elementchen/VoxTriple_Classic/3d_print/Thin/cover.stl

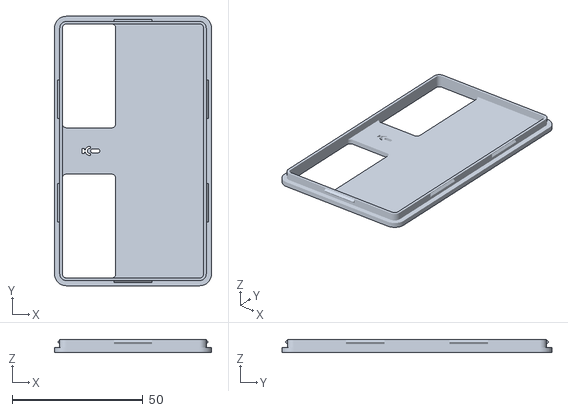
[picture p15: CAD file, 2026-09-11]
3d_print/Thin/cover.stl
60.0 x 103.0 x 5.00
