elementchen/VoxTriple_Classic/3d_print/Minimal/test1.stl

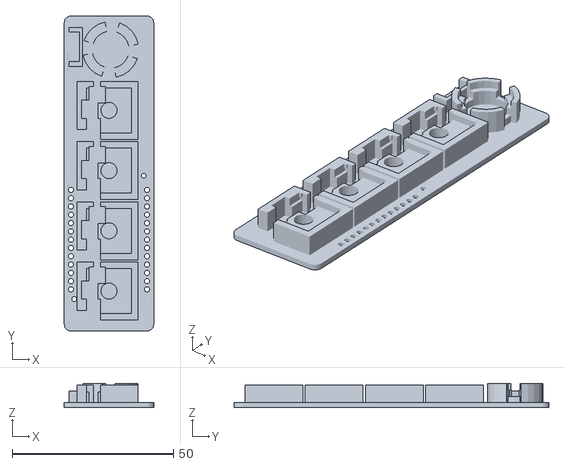
[picture p16: CAD file, 2026-09-13]
3d_print/Minimal/test1.stl
27.8 x 97.8 x 7.50
