elementchen/VoxTriple_Classic/3d_print/Thin/cover_3.stl

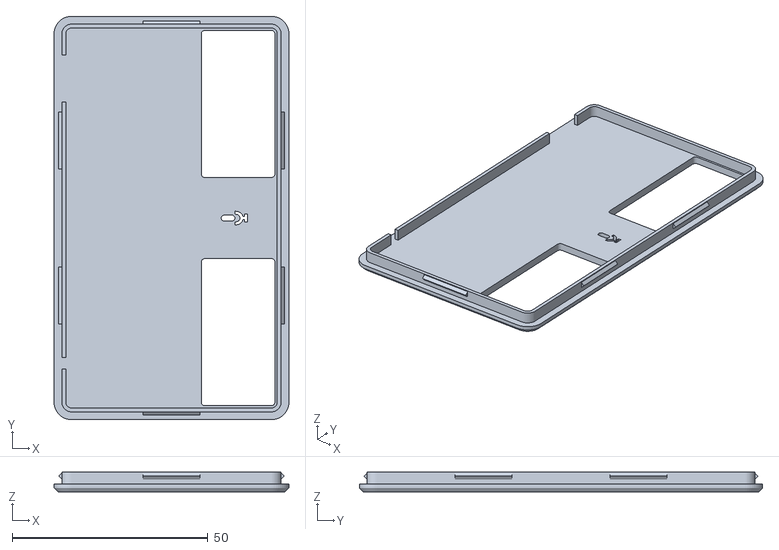
[picture p17: CAD file, 2026-09-11]
3d_print/Thin/cover_3.stl
60.0 x 103.0 x 5.00
