elementchen/VoxTriple_Classic/3d_print/Minimal/test0.stl

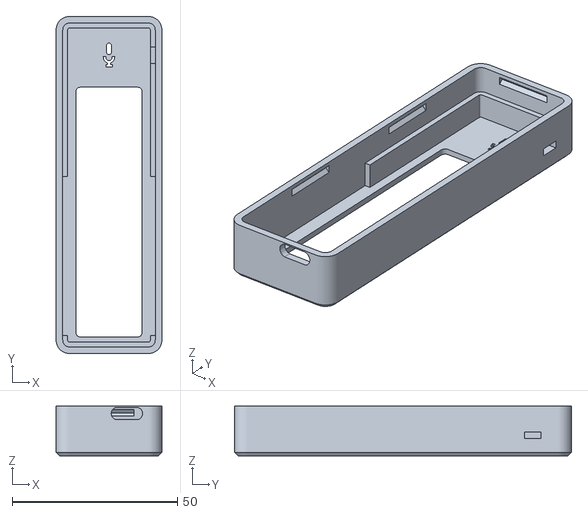
[picture p18: CAD file, 2026-09-13]
3d_print/Minimal/test0.stl
32.0 x 102.0 x 15.0
