elementchen/VoxTriple_Classic/3d_print/Thin/cover_tilt_2.stl

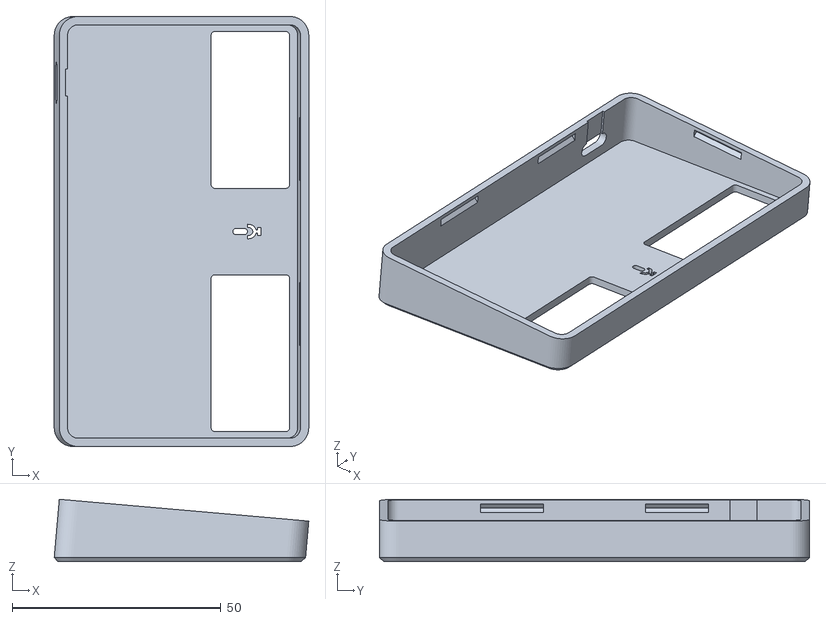
[picture p19: CAD file, 2026-09-11]
3d_print/Thin/cover_tilt_2.stl
61.0 x 103.0 x 15.0
