elementchen/VoxTriple_Classic/3d_print/Minimal/test_all.3mf

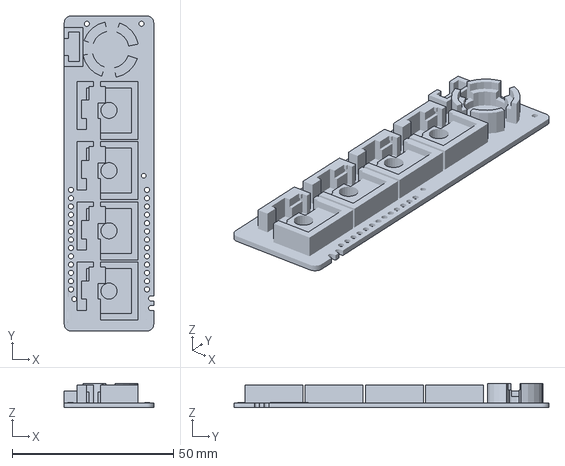
[picture p20: CAD file, 2026-09-13]
3d_print/Minimal/test_all.3mf
27.8 x 97.8 x 7.50 mm
