elementchen/VoxTriple_Classic/3d_print/Minimal/test3.stl

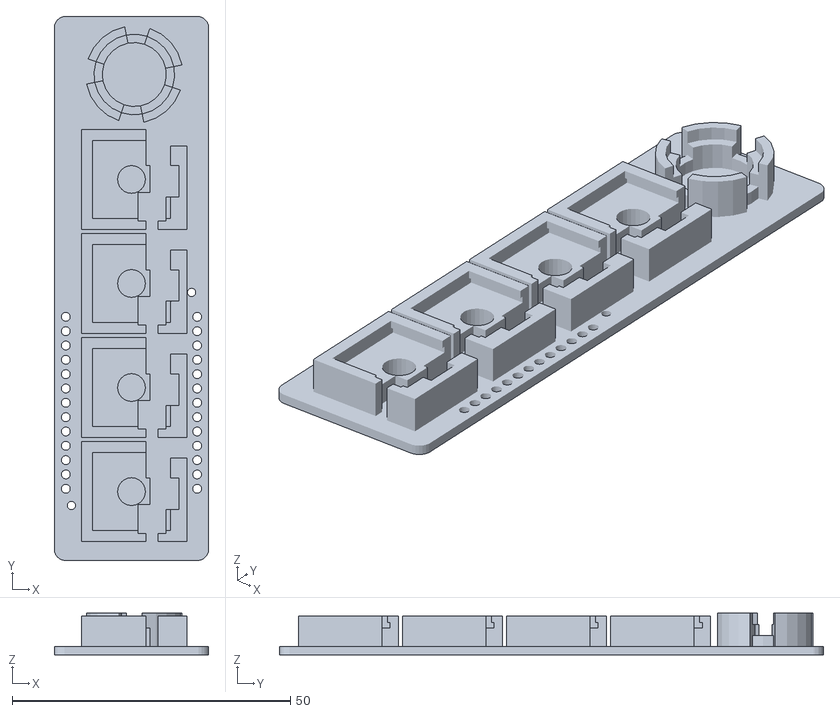
[picture p21: CAD file, 2026-09-11]
3d_print/Minimal/test3.stl
27.8 x 97.8 x 7.50
