elementchen/VoxTriple_Classic/3d_print/Minimal/test.3mf

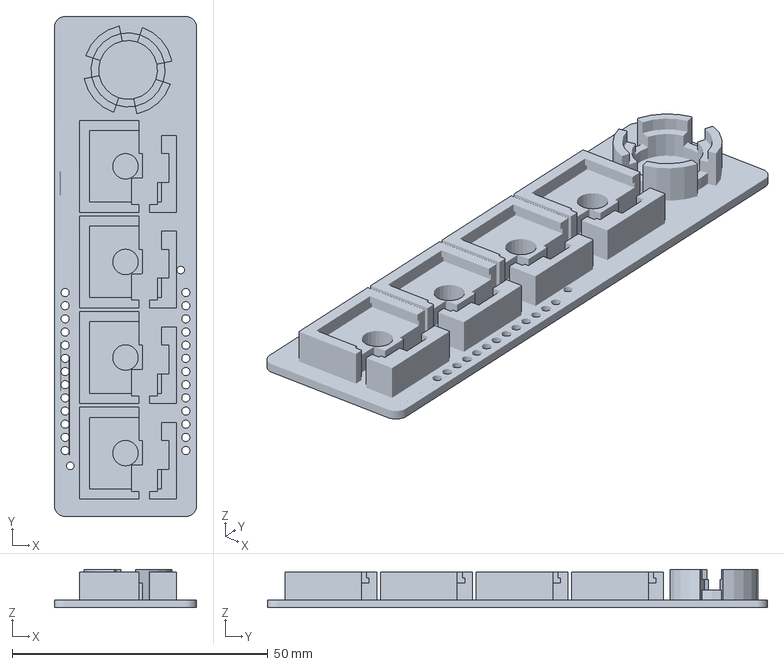
[picture p22: CAD file, 2026-09-11]
3d_print/Minimal/test.3mf
27.8 x 97.8 x 7.50 mm
