elementchen/VoxTriple_Classic/3d_print/Minimal/test2.stl

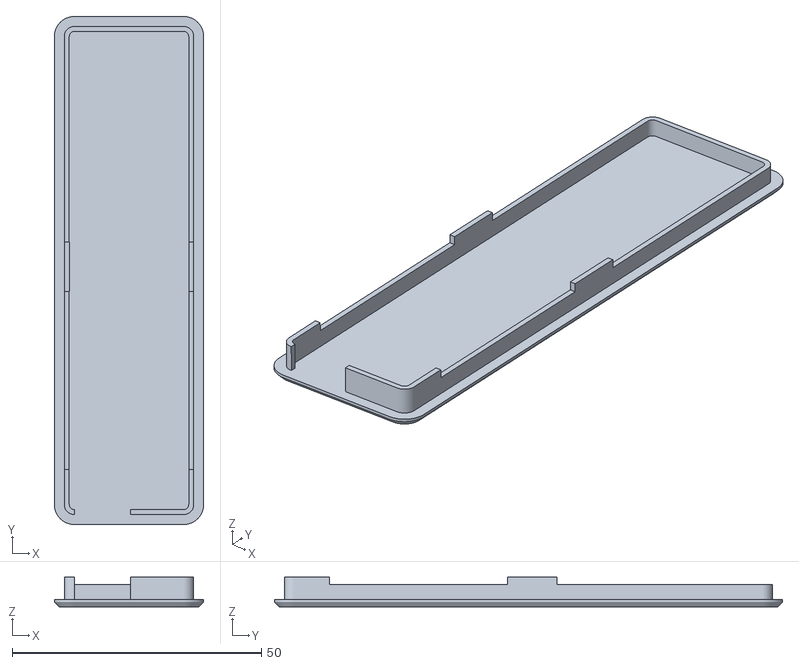
[picture p23: CAD file, 2026-09-11]
3d_print/Minimal/test2.stl
30.0 x 102.0 x 6.02
