elementchen/VoxTriple_Classic/esp32_bt_mic/src/config_storage.c

/*
 * SPDX-FileCopyrightText: 2024 ESP32 BT Microphone Project
 *
 * SPDX-License-Identifier: Unlicense OR CC0-1.0
 */

#include <stdint.h>
#include <string.h>
#include "nvs.h"
#include "nvs_flash.h"
#include "esp_log.h"
#include "config_storage.h"

static const char *TAG = "CONFIG_STORAGE";

/* Default button mappings (Windows VK codes) */
static const uint8_t s_default_vk[BUTTON_NUM] = {
    0x0D,  /* VK_RETURN (Enter) */
    0x1B,  /* VK_ESCAPE (Esc) */
    0x20,  /* VK_SPACE (Space) */
    0x09,  /* VK_TAB (Tab) */
};

static const uint8_t s_default_mod[BUTTON_NUM] = {
    0x00,  /* No modifier */
    0x00,
    0x00,
    0x00,
};

static const char *s_nvs_keys[BUTTON_NUM] = {
    NVS_KEY_BTN1_MAP,
    NVS_KEY_BTN2_MAP,
    NVS_KEY_BTN3_MAP,
    NVS_KEY_BTN4_MAP,
};

void config_storage_init(void)
{
    ESP_LOGI(TAG, "Initializing configuration storage");

    /* Try to load each button mapping; if not found, save defaults */
    for (int i = 0; i < BUTTON_NUM; i++) {
        uint8_t vk_code = 0, modifier = 0;
        esp_err_t ret = config_storage_load_button(i, &vk_code, &modifier);
        if (ret != ESP_OK) {
            ESP_LOGI(TAG, "Button %d: no saved config, setting defaults (VK=0x%02X, MOD=0x%02X)",
                     i + 1, s_default_vk[i], s_default_mod[i]);
            config_storage_save_button(i, s_default_vk[i], s_default_mod[i]);
        } else {
            ESP_LOGI(TAG, "Button %d: loaded config (VK=0x%02X, MOD=0x%02X)",
                     i + 1, vk_code, modifier);
        }
    }

    /* Initialize sleep_mode default configuration (default to 1) */
    uint8_t sleep_mode = 0;
    if (config_storage_load_sleep_mode(&sleep_mode) != ESP_OK) {
        ESP_LOGI(TAG, "Sleep mode: no saved config, setting default (enabled)");
        config_storage_save_sleep_mode(1);
    }

    /* Initialize mic_enabled default configuration (default to 1) */
    uint8_t mic_enabled = 0;
    if (config_storage_load_mic_enabled(&mic_enabled) != ESP_OK) {
        ESP_LOGI(TAG, "Mic enabled: no saved config, setting default (enabled)");
        config_storage_save_mic_enabled(1);
    }
}

esp_err_t config_storage_save_button(uint8_t button_id, uint8_t vk_code, uint8_t modifier)
{
    if (button_id >= BUTTON_NUM) {
        return ESP_ERR_INVALID_ARG;
    }

    nvs_handle_t nvs_handle;
    esp_err_t ret = nvs_open(NVS_NAMESPACE, NVS_READWRITE, &nvs_handle);
    if (ret != ESP_OK) {
        ESP_LOGE(TAG, "NVS open failed: %s", esp_err_to_name(ret));
        return ret;
    }

    /* Store as 2-byte blob: [vk_code, modifier] */
    uint8_t data[2] = {vk_code, modifier};
    ret = nvs_set_blob(nvs_handle, s_nvs_keys[button_id], data, sizeof(data));

    if (ret == ESP_OK) {
        ret = nvs_commit(nvs_handle);
    }

    nvs_close(nvs_handle);

    if (ret != ESP_OK) {
        ESP_LOGE(TAG, "NVS save button %d failed: %s", button_id + 1, esp_err_to_name(ret));
    } else {
        ESP_LOGI(TAG, "Saved button %d mapping: VK=0x%02X, MOD=0x%02X",
                 button_id + 1, vk_code, modifier);
    }

    return ret;
}

esp_err_t config_storage_load_button(uint8_t button_id, uint8_t *vk_code, uint8_t *modifier)
{
    if (button_id >= BUTTON_NUM || !vk_code || !modifier) {
        return ESP_ERR_INVALID_ARG;
    }

    nvs_handle_t nvs_handle;
    esp_err_t ret = nvs_open(NVS_NAMESPACE, NVS_READONLY, &nvs_handle);
    if (ret != ESP_OK) {
        ESP_LOGW(TAG, "NVS open failed: %s", esp_err_to_name(ret));
        return ret;
    }

    uint8_t data[2] = {0, 0};
    size_t length = sizeof(data);

    ret = nvs_get_blob(nvs_handle, s_nvs_keys[button_id], data, &length);
    if (ret == ESP_OK && length == sizeof(data)) {
        *vk_code = data[0];
        *modifier = data[1];
    } else {
        *vk_code = s_default_vk[button_id];
        *modifier = s_default_mod[button_id];
    }

    nvs_close(nvs_handle);
    return ret;
}

#define NVS_KEY_HFP_ADDR "hfp_addr"

esp_err_t config_storage_save_hfp_addr(esp_bd_addr_t addr)
{
    nvs_handle_t nvs_handle;
    esp_err_t ret = nvs_open(NVS_NAMESPACE, NVS_READWRITE, &nvs_handle);
    if (ret != ESP_OK) return ret;

    ret = nvs_set_blob(nvs_handle, NVS_KEY_HFP_ADDR, addr, ESP_BD_ADDR_LEN);
    if (ret == ESP_OK) nvs_commit(nvs_handle);
    nvs_close(nvs_handle);

    if (ret == ESP_OK) {
        ESP_LOGI(TAG, "HFP addr saved: %02x:%02x:%02x:%02x:%02x:%02x",
                 addr[0], addr[1], addr[2], addr[3], addr[4], addr[5]);
    }
    return ret;
}

esp_err_t config_storage_load_hfp_addr(esp_bd_addr_t addr)
{
    nvs_handle_t nvs_handle;
    esp_err_t ret = nvs_open(NVS_NAMESPACE, NVS_READONLY, &nvs_handle);
    if (ret != ESP_OK) return ret;

    size_t len = ESP_BD_ADDR_LEN;
    ret = nvs_get_blob(nvs_handle, NVS_KEY_HFP_ADDR, addr, &len);
    nvs_close(nvs_handle);
    return ret;
}

esp_err_t config_storage_clear_hfp_addr(void)
{
    nvs_handle_t nvs_handle;
    esp_err_t ret = nvs_open(NVS_NAMESPACE, NVS_READWRITE, &nvs_handle);
    if (ret != ESP_OK) return ret;

    ret = nvs_erase_key(nvs_handle, NVS_KEY_HFP_ADDR);
    if (ret == ESP_OK || ret == ESP_ERR_NVS_NOT_FOUND) {
        nvs_commit(nvs_handle);
        ret = ESP_OK;
    }
    nvs_close(nvs_handle);
    ESP_LOGI(TAG, "HFP host address cleared from NVS.");
    return ret;
}

#define NVS_KEY_TX_POWER   "tx_power"
#define NVS_KEY_SLEEP_MODE "sleep_mode"

esp_err_t config_storage_save_tx_power(uint8_t level)
{
    nvs_handle_t nvs_handle;
    esp_err_t ret = nvs_open(NVS_NAMESPACE, NVS_READWRITE, &nvs_handle);
    if (ret != ESP_OK) return ret;

    ret = nvs_set_u8(nvs_handle, NVS_KEY_TX_POWER, level);
    if (ret == ESP_OK) nvs_commit(nvs_handle);
    nvs_close(nvs_handle);

    if (ret == ESP_OK) {
        ESP_LOGI(TAG, "TX power level saved: %d", level);
    }
    return ret;
}

esp_err_t config_storage_load_tx_power(uint8_t *level)
{
    if (!level) return ESP_ERR_INVALID_ARG;

    nvs_handle_t nvs_handle;
    esp_err_t ret = nvs_open(NVS_NAMESPACE, NVS_READONLY, &nvs_handle);
    if (ret != ESP_OK) return ret;

    ret = nvs_get_u8(nvs_handle, NVS_KEY_TX_POWER, level);
    nvs_close(nvs_handle);
    return ret;
}

esp_err_t config_storage_save_sleep_mode(uint8_t enabled)
{
    nvs_handle_t nvs_handle;
    esp_err_t ret = nvs_open(NVS_NAMESPACE, NVS_READWRITE, &nvs_handle);
    if (ret != ESP_OK) return ret;

    ret = nvs_set_u8(nvs_handle, NVS_KEY_SLEEP_MODE, enabled);
    if (ret == ESP_OK) nvs_commit(nvs_handle);
    nvs_close(nvs_handle);

    if (ret == ESP_OK) {
        ESP_LOGI(TAG, "Sleep mode saved: %s", enabled ? "enabled" : "disabled");
    }
    return ret;
}

esp_err_t config_storage_load_sleep_mode(uint8_t *enabled)
{
    if (!enabled) return ESP_ERR_INVALID_ARG;

    nvs_handle_t nvs_handle;
    esp_err_t ret = nvs_open(NVS_NAMESPACE, NVS_READONLY, &nvs_handle);
    if (ret != ESP_OK) return ret;

    ret = nvs_get_u8(nvs_handle, NVS_KEY_SLEEP_MODE, enabled);
    nvs_close(nvs_handle);
    return ret;
}

esp_err_t config_storage_save_mic_enabled(uint8_t enabled)
{
    nvs_handle_t nvs_handle;
    esp_err_t ret = nvs_open(NVS_NAMESPACE, NVS_READWRITE, &nvs_handle);
    if (ret != ESP_OK) return ret;

    ret = nvs_set_u8(nvs_handle, NVS_KEY_MIC_ENABLED, enabled);
    if (ret == ESP_OK) nvs_commit(nvs_handle);
    nvs_close(nvs_handle);
    if (ret == ESP_OK) {
        ESP_LOGI(TAG, "Mic enabled configuration saved: %d", enabled);
    }
    return ret;
}

esp_err_t config_storage_load_mic_enabled(uint8_t *enabled)
{
    if (!enabled) return ESP_ERR_INVALID_ARG;

    nvs_handle_t nvs_handle;
    esp_err_t ret = nvs_open(NVS_NAMESPACE, NVS_READONLY, &nvs_handle);
    if (ret != ESP_OK) return ret;

    ret = nvs_get_u8(nvs_handle, NVS_KEY_MIC_ENABLED, enabled);
    nvs_close(nvs_handle);
    return ret;
}

esp_err_t config_storage_clear_all(void)
{
    nvs_handle_t nvs_handle;
    esp_err_t ret = nvs_open(NVS_NAMESPACE, NVS_READWRITE, &nvs_handle);
    if (ret != ESP_OK) return ret;

    ret = nvs_erase_all(nvs_handle);
    if (ret == ESP_OK) nvs_commit(nvs_handle);
    nvs_close(nvs_handle);
    ESP_LOGI(TAG, "Config storage cleared successfully.");
    return ret;
}

esp_err_t config_storage_save_ota_ready(uint8_t ready)
{
    nvs_handle_t nvs_handle;
    esp_err_t ret = nvs_open(NVS_NAMESPACE, NVS_READWRITE, &nvs_handle);
    if (ret != ESP_OK) return ret;

    ret = nvs_set_u8(nvs_handle, NVS_KEY_OTA_READY, ready);
    if (ret == ESP_OK) nvs_commit(nvs_handle);
    nvs_close(nvs_handle);
    if (ret == ESP_OK) {
        ESP_LOGI(TAG, "OTA Ready flag saved: %d", ready);
    }
    return ret;
}

esp_err_t config_storage_load_ota_ready(uint8_t *ready)
{
    if (!ready) return ESP_ERR_INVALID_ARG;

    nvs_handle_t nvs_handle;
    esp_err_t ret = nvs_open(NVS_NAMESPACE, NVS_READONLY, &nvs_handle);
    if (ret != ESP_OK) return ret;

    ret = nvs_get_u8(nvs_handle, NVS_KEY_OTA_READY, ready);
    nvs_close(nvs_handle);
    return ret;
}

esp_err_t config_storage_save_board_model(uint8_t model)
{
    nvs_handle_t nvs_handle;
    esp_err_t ret = nvs_open(NVS_NAMESPACE, NVS_READWRITE, &nvs_handle);
    if (ret != ESP_OK) return ret;

    ret = nvs_set_u8(nvs_handle, NVS_KEY_BOARD_MODEL, model);
    if (ret == ESP_OK) nvs_commit(nvs_handle);
    nvs_close(nvs_handle);
    if (ret == ESP_OK) {
        ESP_LOGI(TAG, "Board model saved: %d", model);
    }
    return ret;
}

esp_err_t config_storage_load_board_model(uint8_t *model)
{
    if (!model) return ESP_ERR_INVALID_ARG;

    nvs_handle_t nvs_handle;
    esp_err_t ret = nvs_open(NVS_NAMESPACE, NVS_READONLY, &nvs_handle);
    if (ret != ESP_OK) return ret;

    ret = nvs_get_u8(nvs_handle, NVS_KEY_BOARD_MODEL, model);
    nvs_close(nvs_handle);
    return ret;
}

esp_err_t config_storage_save_sleep_timeout(uint8_t minutes)
{
    nvs_handle_t nvs_handle;
    esp_err_t ret = nvs_open(NVS_NAMESPACE, NVS_READWRITE, &nvs_handle);
    if (ret != ESP_OK) return ret;

    ret = nvs_set_u8(nvs_handle, NVS_KEY_SLEEP_TIMEOUT, minutes);
    if (ret == ESP_OK) nvs_commit(nvs_handle);
    nvs_close(nvs_handle);
    if (ret == ESP_OK) {
        ESP_LOGI(TAG, "Sleep timeout saved: %d min", minutes);
    }
    return ret;
}

esp_err_t config_storage_load_sleep_timeout(uint8_t *minutes)
{
    if (!minutes) return ESP_ERR_INVALID_ARG;

    nvs_handle_t nvs_handle;
    esp_err_t ret = nvs_open(NVS_NAMESPACE, NVS_READONLY, &nvs_handle);
    if (ret != ESP_OK) return ret;

    ret = nvs_get_u8(nvs_handle, NVS_KEY_SLEEP_TIMEOUT, minutes);
    nvs_close(nvs_handle);
    return ret;
}
