elementchen/VoxTriple_Classic/windows_app_python/spp_client.py

"""Classic Bluetooth SPP Client for VoxTriple.

Replaces the BleClient (ble_client.py) using pyserial.
Bridges serial sync-read thread to asyncio futures for smooth GUI interaction.
"""
import os
import sys
import re
import asyncio
import json
import logging
import threading
import serial
import serial.tools.list_ports

log = logging.getLogger(__name__)


class _EsptoolProgressWriter:
    """Captures esptool stdout to extract flash write percentage and invoke GUI progress callback."""
    def __init__(self, orig_stdout, total_size, cb=None):
        self.orig_stdout = orig_stdout
        self.total_size = total_size
        self.cb = cb
        self.pct_re = re.compile(r'\((\d+)\s*%\)')
        self.encoding = getattr(orig_stdout, "encoding", "utf-8") or "utf-8"
        self.errors = getattr(orig_stdout, "errors", "replace") or "replace"

    def isatty(self):
        return False

    def write(self, text):
        if self.orig_stdout:
            try:
                self.orig_stdout.write(text)
            except Exception:
                pass
        m = self.pct_re.search(text)
        if m:
            pct = int(m.group(1))
            if self.cb:
                written = int(self.total_size * pct / 100)
                try:
                    self.cb(written, self.total_size)
                except Exception:
                    pass

    def flush(self):
        if self.orig_stdout:
            try:
                self.orig_stdout.flush()
            except Exception:
                pass


class SppClient:
    """Connects to ESP32 SPP server via virtual COM port."""

    def __init__(self):
        self._ser = None
        self._port = None
        self._connected = False
        self._read_thread = None
        self._loop = None
        
        # Callbacks registered by the GUI
        self.on_button_event = None   # callback(button_id: int, state: int)
        self.on_status = None         # callback(hfp: int, audio: int)

        # Future used to wait for responses of commands
        self._response_future = None
        
        # Local configuration cache populated on connection
        self._config_cache = {}
        
        # OTA mode flag and queue for flow control
        self._ota_mode = False
        self._ota_queue = asyncio.Queue()

    @property
    def is_connected(self) -> bool:
        return self._connected

    @property
    def address(self) -> str | None:
        """Expose the current COM port name to mimic the original BLE address API."""
        return self._port

    @staticmethod
    def list_ports() -> list[dict]:
        """List all COM ports, sorting likely Bluetooth ports to the top."""
        ports = serial.tools.list_ports.comports()
        result = []
        for p in ports:
            name = p.device
            desc = p.description or ""
            hwid = p.hwid or ""
            
            # Identify potential bluetooth virtual serial ports
            is_bt = False
            bt_keywords = ["bluetooth", "btport", "bthenum", "蓝牙", "标准串行"]
            if any(kw in desc.lower() or kw in hwid.lower() for kw in bt_keywords):
                is_bt = True
                
            result.append({
                "port": name,
                "desc": f"{name} ({desc})",
                "is_bt": is_bt
            })
            
        # Sort so that Bluetooth ports appear first
        result.sort(key=lambda x: x["is_bt"], reverse=True)
        return result

    async def connect(self, port: str) -> bool:
        """Open the serial port, start the read thread, and fetch configuration."""
        try:
            log.info(f"Connecting to serial port {port}...")
            # Configure PySerial without triggering auto-reset flags where supported
            self._ser = serial.Serial()
            self._ser.port = port
            self._ser.baudrate = 115200
            self._ser.timeout = 1.0
            self._ser.rtscts = False
            self._ser.dsrdtr = False
            self._ser.open()
            
            # Explicitly clear DTR and RTS pin levels to try avoiding ESP32 reset
            try:
                self._ser.dtr = False
                self._ser.rts = False
            except Exception:
                pass
                
            self._port = port
            self._connected = True
            
            # Capture the current asyncio event loop to dispatch events safely
            self._loop = asyncio.get_running_loop()
            
            # Start background reading thread
            self._read_thread = threading.Thread(target=self._run_read_loop, daemon=True)
            self._read_thread.start()
            
            # Delay to wait for ESP32 boot sequence to finish if reset was triggered
            log.info("Waiting 2.5 seconds for device boot stabilization...")
            await asyncio.sleep(2.5)
            
            # Fetch device configuration to populate cache
            ok = await self._fetch_config()
            if not ok:
                log.warning("Failed to fetch initial configuration from device.")
                # We still keep the connection, it might have been a timeout
                
            log.info(f"SPP Client successfully connected to {port}")
            return True
        except Exception as e:
            log.error(f"Failed to connect to {port}: {e}")
            self.disconnect_sync()
            return False

    async def disconnect(self):
        """Asynchronous disconnect wrapper."""
        self.disconnect_sync()

    def disconnect_sync(self):
        """Synchronously close the port and join reader thread."""
        self._connected = False
        if self._ser:
            try:
                self._ser.close()
            except Exception:
                pass
            self._ser = None
        self._port = None
        self._config_cache.clear()
        log.info("SPP Client disconnected")

    def _run_read_loop(self):
        """Thread worker to continuously read from the serial port line by line."""
        while self._connected and self._ser:
            try:
                line_bytes = self._ser.readline()
                if not line_bytes:
                    continue
                    
                line = line_bytes.decode("utf-8", errors="ignore").strip()
                if not line:
                    continue
                    
                log.debug(f"Serial RX: {line}")
                if not line.startswith("{"):
                    log.warning(f"[ESP32 LOG] {line}")
                    continue
                try:
                    data = json.loads(line)
                except json.JSONDecodeError:
                    # Robust fallback parser for noisy serial lines (crosstalk / power ripple bit-flips)
                    import re
                    recovered = False
                    data = {}
                    if "next" in line:
                        tw_match = re.search(r'"total_written"\s*:\s*(\d+)', line)
                        if tw_match:
                            data = {"status": "next", "total_written": int(tw_match.group(1))}
                            recovered = True
                    elif "done" in line:
                        data = {"status": "done"}
                        recovered = True
                    elif "error" in line:
                        data = {"status": "error"}
                        reason_match = re.search(r'"reason"\s*:\s*"([^"]+)"', line)
                        data["reason"] = reason_match.group(1) if reason_match else "unknown_recovered"
                        recovered = True
                        
                    if recovered:
                        log.warning(f"Recovered JSON structure from noisy line: {line} -> {data}")
                    else:
                        log.warning(f"[ESP32 LOG (JSON Parse Fail)] {line}")
                        continue
                
                # Check if it's an unsolicited event from ESP32
                if "event" in data:
                    evt = data["event"]
                    if evt == "btn" and self.on_button_event:
                        btn_id = data.get("id", 0)
                        state = data.get("state", 0)
                        self.on_button_event(btn_id, state)
                    elif evt == "status" and self.on_status:
                        hfp = data.get("hfp", 0)
                        audio = data.get("audio", 0)
                        self.on_status(hfp, audio)
                        
                # Check if it's a command response
                elif "status" in data:
                    if self._ota_mode:
                        self._loop.call_soon_threadsafe(self._ota_queue.put_nowait, data)
                    else:
                        # Dispatch to the waiting future with race condition protection
                        fut = self._response_future
                        if fut and not fut.done():
                            self._response_future = None  # Block subsequent arrivals from touching this future
                            self._loop.call_soon_threadsafe(fut.set_result, data)
                        
            except Exception as e:
                log.error(f"Error in read loop: {e}")
                if self._connected:
                    # Trigger disconnect in case of hardware error
                    self._loop.call_soon_threadsafe(self.disconnect_sync)
                break

    async def _send_cmd(self, cmd_dict: dict, timeout: float = 2.0) -> dict | None:
        """Send a JSON command and wait asynchronously for its response."""
        if not self._connected or not self._ser:
            return None
            
        # Create a new future for this command
        self._response_future = self._loop.create_future()
        
        try:
            cmd_str = json.dumps(cmd_dict) + "\n"
            self._ser.write(cmd_str.encode("utf-8"))
            
            # Wait for response future to resolve
            resp = await asyncio.wait_for(self._response_future, timeout=timeout)
            return resp
        except Exception as e:
            log.error(f"Command {cmd_dict.get('cmd')} failed: {e}")
            return None
        finally:
            self._response_future = None

    async def _fetch_config(self) -> bool:
        """Fetch the full configuration from ESP32 and save in cache."""
        for attempt in range(3):
            log.info(f"Fetching configuration from device (attempt {attempt + 1}/3)...")
            resp = await self._send_cmd({"cmd": "get_config"}, timeout=1.5)
            if resp and resp.get("status") == "ok":
                self._config_cache = resp
                return True
            await asyncio.sleep(1.0)
        return False

    async def read_button_mapping(self, idx: int) -> tuple[int, int] | None:
        """Return the (vk_code, modifier) for button index from cache."""
        # Use cached values. If not cached, attempt a fetch
        if not self._config_cache:
            await self._fetch_config()
            
        vk_key = f"btn{idx+1}_vk"
        mod_key = f"btn{idx+1}_mod"
        
        if vk_key in self._config_cache and mod_key in self._config_cache:
            return self._config_cache[vk_key], self._config_cache[mod_key]
        return None

    async def write_button_mapping(self, idx: int, vk: int, mod: int) -> bool:
        """Send command to save button mapping on the ESP32."""
        resp = await self._send_cmd({
            "cmd": "set_btn",
            "idx": idx,
            "vk": vk,
            "mod": mod
        })
        if resp and resp.get("status") == "ok":
            # Update local cache
            self._config_cache[f"btn{idx+1}_vk"] = vk
            self._config_cache[f"btn{idx+1}_mod"] = mod
            return True
        return False

    async def read_tx_power(self) -> int | None:
        """Get the Classic BT TX power level from cache."""
        if not self._config_cache:
            await self._fetch_config()
        return self._config_cache.get("tx_power")

    async def write_tx_power(self, level: int) -> bool:
        """Save Classic BT TX power level to the ESP32."""
        resp = await self._send_cmd({
            "cmd": "set_tx_power",
            "level": level
        })
        if resp and resp.get("status") == "ok":
            self._config_cache["tx_power"] = level
            return True
        return False

    async def read_sleep_mode(self) -> int | None:
        """Get the sleep mode enabled flag from cache."""
        if not self._config_cache:
            await self._fetch_config()
        return self._config_cache.get("sleep_mode")

    async def write_sleep_mode(self, enabled: int) -> bool:
        """Save sleep mode configuration to the ESP32."""
        resp = await self._send_cmd({
            "cmd": "set_sleep_mode",
            "enabled": enabled
        })
        if resp and resp.get("status") == "ok":
            self._config_cache["sleep_mode"] = enabled
            return True
        return False

    async def read_mic_enabled(self) -> int | None:
        """Get the mic enabled flag from cache."""
        if not self._config_cache:
            await self._fetch_config()
        return self._config_cache.get("mic_enabled")

    async def write_mic_enabled(self, enabled: int) -> bool:
        """Save mic enabled configuration to the ESP32."""
        resp = await self._send_cmd({
            "cmd": "set_mic_enabled",
            "enabled": enabled
        })
        if resp and resp.get("status") == "ok":
            self._config_cache["mic_enabled"] = enabled
            return True
        return False

    async def read_board_model(self) -> int | None:
        """Get the hardware board model from cache (0: WEMOS 18650, 1: ESP32 Lite V1.0.0)."""
        if not self._config_cache:
            await self._fetch_config()
        return self._config_cache.get("board_model", 0)

    async def write_board_model(self, model: int) -> bool:
        """Save hardware board model to the ESP32 and trigger reboot."""
        resp = await self._send_cmd({
            "cmd": "set_board_model",
            "model": model
        })
        if resp and resp.get("status") == "ok":
            self._config_cache["board_model"] = model
            return True
        return False

    async def read_sleep_timeout_min(self) -> int | None:
        """Get the inactivity deep sleep timeout (in minutes) from cache."""
        if not self._config_cache:
            await self._fetch_config()
        return self._config_cache.get("sleep_timeout_min", 5)

    async def write_sleep_timeout_min(self, minutes: int) -> bool:
        """Save inactivity sleep timeout (minutes) to the ESP32 and trigger reboot."""
        resp = await self._send_cmd({
            "cmd": "set_sleep_timeout",
            "minutes": minutes
        })
        if resp and resp.get("status") == "ok":
            self._config_cache["sleep_timeout_min"] = minutes
            return True
        return False

    async def reset_bt_pairing(self) -> bool:
        """Send command to reset Bluetooth pairings on ESP32 (forget device & reboot)."""
        resp = await self._send_cmd({"cmd": "reset_bt_pairing"})
        return resp is not None and resp.get("status") == "ok"

    async def get_config(self) -> dict | None:
        """Fetch and return full configuration dictionary formatted for UI client."""
        ok = await self._fetch_config()
        if ok:
            cfg = {
                "buttons": [
                    {"vk": self._config_cache.get("btn1_vk", 0), "mod": self._config_cache.get("btn1_mod", 0)},
                    {"vk": self._config_cache.get("btn2_vk", 0), "mod": self._config_cache.get("btn2_mod", 0)},
                    {"vk": self._config_cache.get("btn3_vk", 0), "mod": self._config_cache.get("btn3_mod", 0)},
                    {"vk": self._config_cache.get("btn4_vk", 0), "mod": self._config_cache.get("btn4_mod", 0)}
                ],
                "tx_power": self._config_cache.get("tx_power", 4),
                "sleep": self._config_cache.get("sleep_mode", 1),
                "mic_enabled": self._config_cache.get("mic_enabled", 1),
                "version": self._config_cache.get("version", "1.0.0"),
                "board_model": self._config_cache.get("board_model", 0),
                "board_name": self._config_cache.get("board_name", "WEMOS 18650"),
                "sleep_timeout_min": self._config_cache.get("sleep_timeout_min", 5)
            }
            return cfg
        return None

    async def set_config(self, mapping: list, tx: int, sleep: int, mic_enabled: int = 1) -> bool:
        """macOS helper to write all configurations at once."""
        for i in range(min(len(mapping), 4)):
            ok = await self.write_button_mapping(i, mapping[i]["vk"], mapping[i]["mod"])
            if not ok:
                return False
        ok = await self.write_tx_power(tx)
        if not ok:
            return False
        ok = await self.write_sleep_mode(sleep)
        if not ok:
            return False
        ok = await self.write_mic_enabled(mic_enabled)
        if not ok:
            return False
        return True

    async def read_firmware_version(self) -> str:
        """Get the current firmware version from cache."""
        if not self._config_cache:
            await self._fetch_config()
        return self._config_cache.get("version", "Unknown")

    async def upload_firmware(self, bin_path: str, progress_callback=None, mode="auto") -> bool:
        """Upload firmware .bin file to ESP32 using direct esptool hardware flash with legacy fallback."""
        if not self._connected or not self._ser:
            log.error("Flash failed: Serial client is not connected.")
            return False

        if not os.path.isfile(bin_path):
            log.error(f"Firmware binary file not found: {bin_path}")
            return False

        total_size = os.path.getsize(bin_path)
        port = self._port or (self._ser.port if self._ser else None)
        log.info(f"Starting firmware upload on {port}. File: {bin_path} ({total_size} bytes, Mode: {mode})")

        has_esptool = False
        try:
            import esptool
            has_esptool = True
        except ImportError:
            log.warning("esptool module not available in environment, falling back to legacy OTA.")

        # If connected via physical serial port and esptool is available, use direct hardware flash
        if has_esptool and port and mode != "legacy":
            log.info("Executing Direct Hardware Flash Engine (Scheme B)...")
            return await self._upload_firmware_esptool(bin_path, total_size, port, progress_callback)
        else:
            log.info("Executing Legacy Chunked OTA Engine...")
            return await self._upload_firmware_legacy(bin_path, total_size, progress_callback)

    async def _upload_firmware_esptool(self, bin_path: str, total_size: int, port: str, progress_callback=None) -> bool:
        """Directly flash ESP32 via esptool Python API, cross-platform compatible with CH340 & CP2102."""
        import esptool

        # Smart flash offset:
        # Full merged image (> 1MB or containing 'merged') flashes at 0x0
        # Single App partition (standard OTA bin ~930KB) flashes at 0x20000
        is_merged = (total_size > 1000000) or ("merged" in os.path.basename(bin_path).lower())
        flash_offset = "0x0" if is_merged else "0x20000"
        log.info(f"Direct Flash: Target flash offset: {flash_offset} (Merged: {is_merged})")

        # 1. Release serial port so esptool has exclusive physical access
        log.info(f"Direct Flash: Closing pyserial handle on {port}...")
        self.disconnect_sync()
        await asyncio.sleep(1.0)

        # 2. Run esptool in thread pool executor to prevent blocking asyncio loop
        loop = asyncio.get_running_loop()

        def do_esptool(baud: int) -> bool:
            old_stdout = sys.stdout
            old_stderr = sys.stderr
            writer = _EsptoolProgressWriter(old_stdout, total_size, progress_callback)
            sys.stdout = writer
            sys.stderr = writer
            args = [
                "--chip", "esp32",
                "--port", port,
                "--baud", str(baud),
                "--before", "default-reset",
                "--after", "hard-reset",
                "write-flash",
                "--flash-mode", "dio",
                "--flash-size", "4MB",
                "--flash-freq", "40m",
                flash_offset, bin_path
            ]
            try:
                log.info(f"Invoking esptool.main on {port} with baud {baud}...")
                esptool.main(args)
                return True
            except SystemExit as se:
                if se.code != 0:
                    self.last_error = f"esptool exit code {se.code}"
                    log.error(f"esptool exited with non-zero exit code: {se.code}")
                return (se.code == 0)
            except Exception as e:
                import traceback
                self.last_error = str(e)
                log.error(f"esptool execution error at {baud} baud: {e}\n{traceback.format_exc()}")
                return False
            finally:
                sys.stdout = old_stdout
                sys.stderr = old_stderr

        # Try high speed 460800 first (takes only ~13s)
        flash_ok = await loop.run_in_executor(None, do_esptool, 460800)
        if not flash_ok:
            log.warning("High-speed 460800 flash attempt failed. Retrying at 115200 baud...")
            await asyncio.sleep(1.0)
            flash_ok = await loop.run_in_executor(None, do_esptool, 115200)

        if not flash_ok:
            log.error(f"Direct esptool flash failed: {getattr(self, 'last_error', 'unknown')}")
            # Attempt to reconnect anyway so GUI remains operational
            await self.connect(port)
            return False

        log.info("Direct flash succeeded! Device is rebooting via hardware reset pulse.")
        if progress_callback:
            try:
                progress_callback(total_size, total_size)
            except Exception:
                pass

        # 3. Wait 2.0s for hardware reset to stabilize and re-establish connection
        await asyncio.sleep(2.0)
        log.info(f"Re-connecting to {port} to restore application link...")
        for retry in range(3):
            if await self.connect(port):
                log.info("Re-connected successfully to device after flash!")
                break
            await asyncio.sleep(1.0)

        return True

    async def _upload_firmware_legacy(self, bin_path: str, total_size: int, progress_callback=None) -> bool:
        """Legacy chunked VFS serial OTA protocol fallback."""
        try:
            with open(bin_path, "rb") as f:
                bin_data = f.read()
        except Exception as e:
            log.error(f"Failed to read firmware binary file: {e}")
            return False

        # Clear any stale data in ota_queue
        while not self._ota_queue.empty():
            self._ota_queue.get_nowait()

        # 1. Send ota_start command
        resp = await self._send_cmd({"cmd": "ota_start", "size": total_size}, timeout=10.0)
        if not resp:
            log.error("OTA start failed: No response from device.")
            return False

        if resp.get("status") == "ok" and resp.get("reboot") == 1:
            log.info("Device is rebooting into clean OTA mode...")
            port = self._ser.port
            await self.disconnect()
            await asyncio.sleep(3.0)
            log.info(f"Reconnecting to {port} in clean OTA mode...")
            if not await self.connect(port):
                log.error("Failed to reconnect in clean OTA mode.")
                return False
            resp = await self._send_cmd({"cmd": "ota_start", "size": total_size}, timeout=10.0)
            if not resp or resp.get("status") != "ok":
                log.error(f"Clean OTA start failed: {resp.get('reason') if resp else 'No response'}")
                return False
        elif resp.get("status") != "ok":
            log.error(f"OTA start failed: {resp.get('reason')}")
            return False

        log.info("OTA handshake success. Transferring binary payload in chunks...")
        self._ota_mode = True
        try:
            chunk_size = 256
            current_total = 0
            for i in range(0, total_size, chunk_size):
                chunk = bin_data[i:i+chunk_size]
                expected_total = i + len(chunk)
                is_last_chunk = (i + chunk_size >= total_size)
                if is_last_chunk and i > 0:
                    target_sync = (i // 1024) * 1024
                    try:
                        while current_total < target_sync:
                            chunk_resp = await asyncio.wait_for(self._ota_queue.get(), timeout=8.0)
                            if chunk_resp:
                                if chunk_resp.get("status") == "error":
                                    return False
                                if chunk_resp.get("status") == "done":
                                    return True
                                current_total = max(current_total, chunk_resp.get("total_written", 0))
                    except asyncio.TimeoutError:
                        return False

                self._ser.write(chunk)
                self._ser.flush()

                while not self._ota_queue.empty():
                    try:
                        chunk_resp = self._ota_queue.get_nowait()
                        if chunk_resp:
                            if chunk_resp.get("status") == "error":
                                return False
                            if chunk_resp.get("status") == "done":
                                return True
                            current_total = max(current_total, chunk_resp.get("total_written", 0))
                    except asyncio.QueueEmpty:
                        break

                if i > 0 and i % (1024 * 16) == 0:
                    target_sync = (i // 1024) * 1024
                    try:
                        while current_total < target_sync:
                            chunk_resp = await asyncio.wait_for(self._ota_queue.get(), timeout=10.0)
                            if chunk_resp:
                                if chunk_resp.get("status") == "error":
                                    return False
                                if chunk_resp.get("status") == "done":
                                    return True
                                current_total = max(current_total, chunk_resp.get("total_written", 0))
                    except asyncio.TimeoutError:
                        return False

                if progress_callback:
                    progress_callback(max(current_total, expected_total), total_size)

                await asyncio.sleep(0.005)

            log.info("All firmware chunks sent. Waiting for final verification on device...")
            try:
                while True:
                    final_resp = await asyncio.wait_for(self._ota_queue.get(), timeout=8.0)
                    if not final_resp:
                        return False
                    status = final_resp.get("status")
                    if status == "done":
                        return True
                    elif status == "error":
                        return False
                    elif status in ("progress", "next"):
                        continue
                    else:
                        return False
            except asyncio.TimeoutError:
                return False
        finally:
            self._ota_mode = False
