elementchen/VoxTriple_Classic/esp32_bt_mic/src/button_handler.h

/*
 * SPDX-FileCopyrightText: 2024 ESP32 BT Microphone Project
 *
 * SPDX-License-Identifier: Unlicense OR CC0-1.0
 */

#ifndef __BUTTON_HANDLER_H__
#define __BUTTON_HANDLER_H__

/**
 * @brief Initialize button GPIO pins and start debounce task
 */
void button_handler_init(void);

/**
 * @brief Deinitialize button handler
 */
void button_handler_deinit(void);

/**
 * @brief Forget paired Bluetooth devices, clear link keys and auto-reconnect MAC, then reboot
 */
void system_reset_bt_pairing(void);

#endif /* __BUTTON_HANDLER_H__ */
